rrrenai/wave/journal_images/11-8-25.png

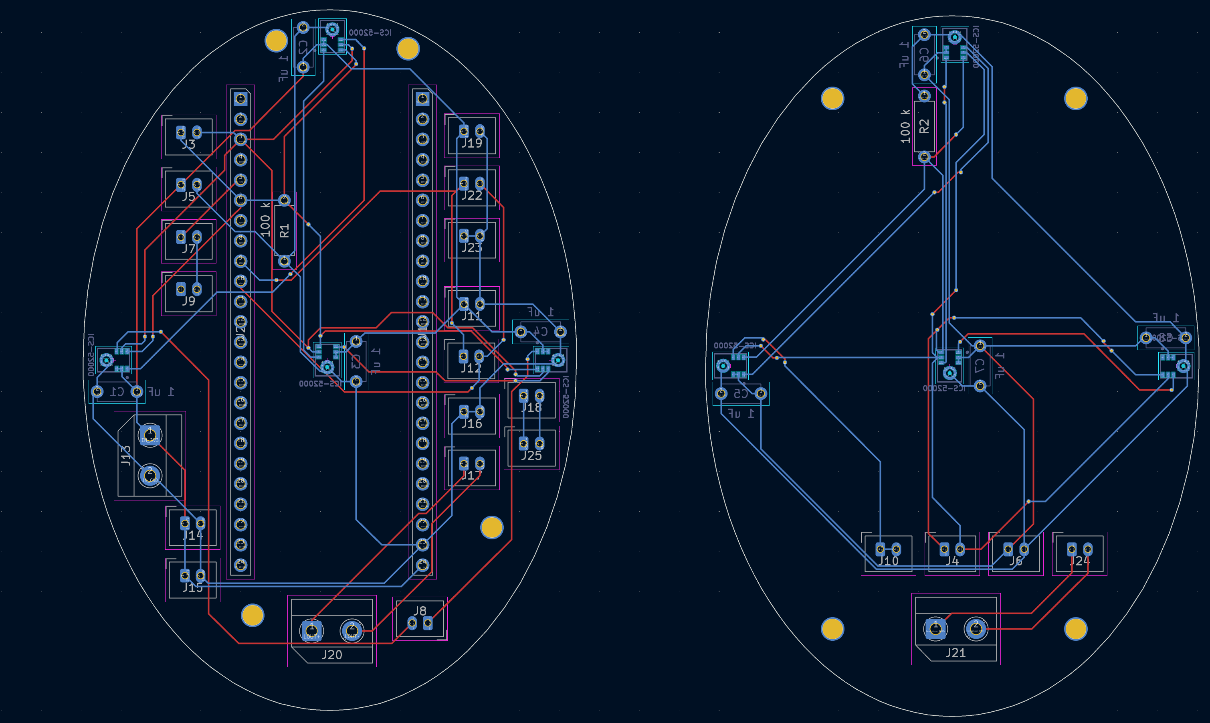
journal_images/11-8-25.png
