rrrenai/wave/journal_images/11-8-25_3d_back.png

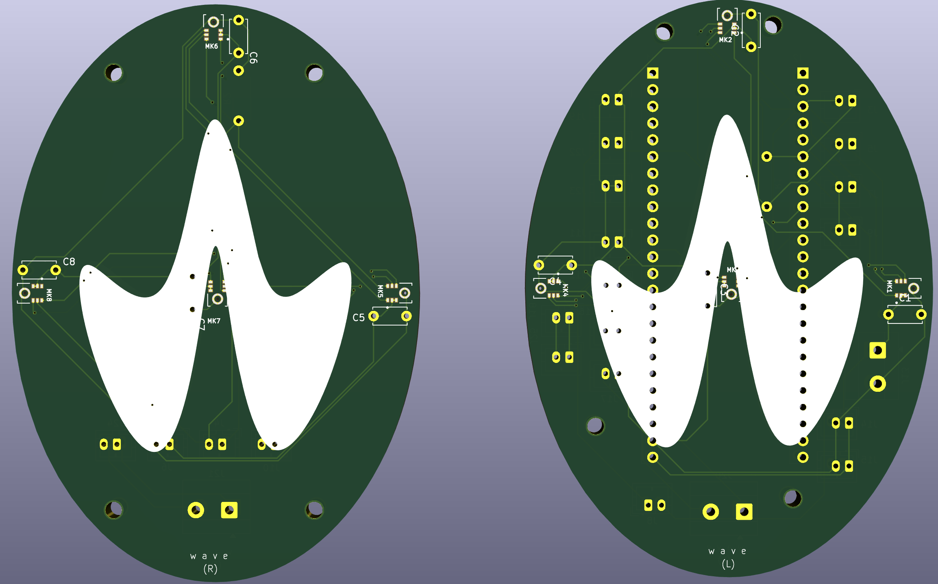
journal_images/11-8-25_3d_back.png
