rrrenai/wave/journal_images/11-20-25.png

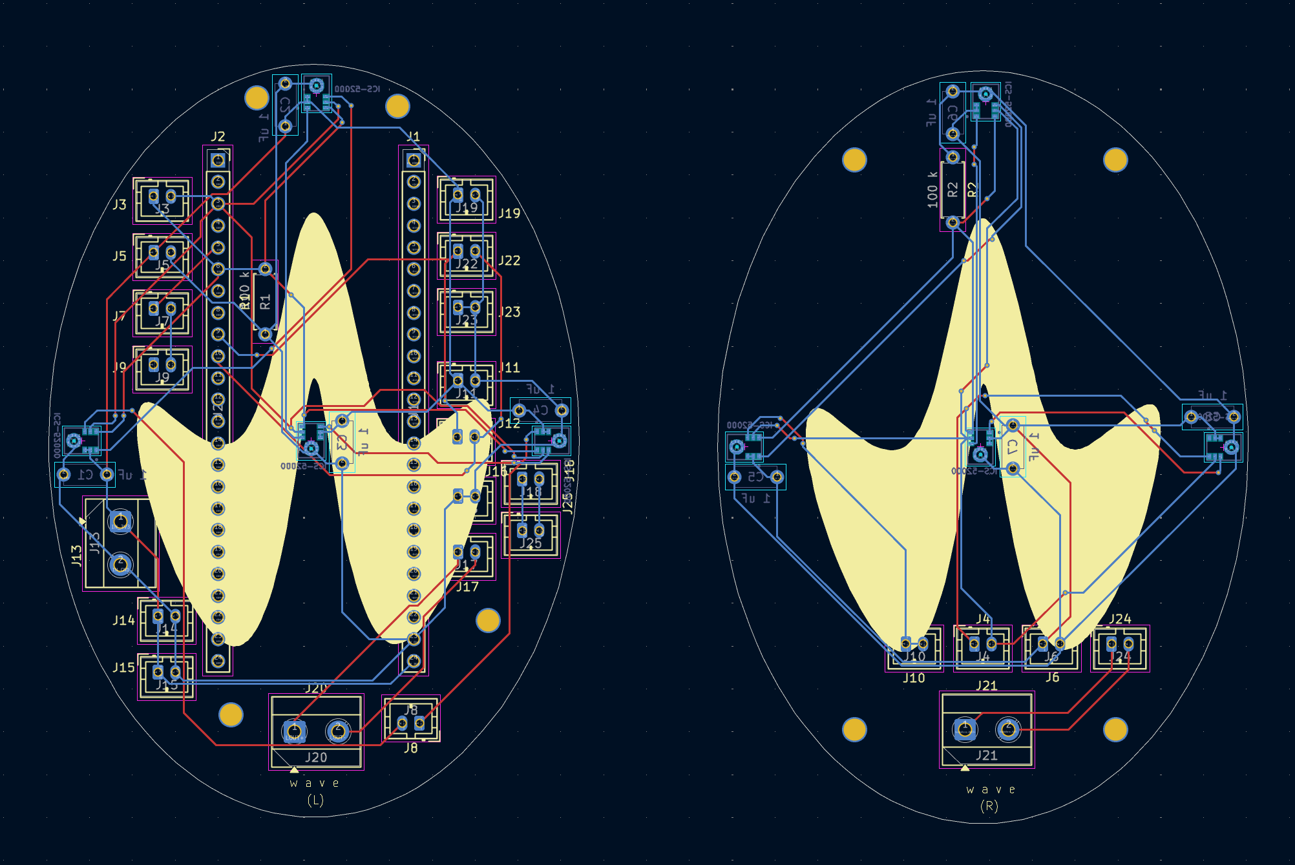
journal_images/11-20-25.png
