rrrenai/wave/journal_images/12-26-25_inner_RIGHT.png

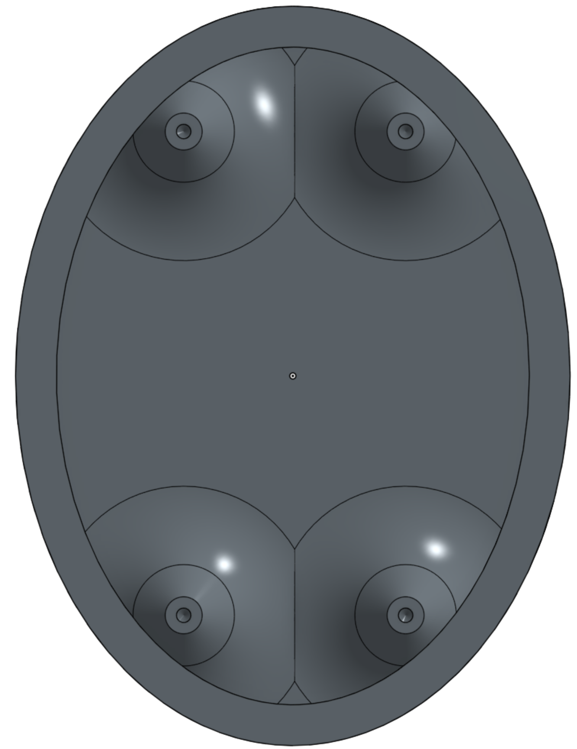
journal_images/12-26-25_inner_RIGHT.png
