rrrenai/wave/journal_images/12-26-25_SNR.png

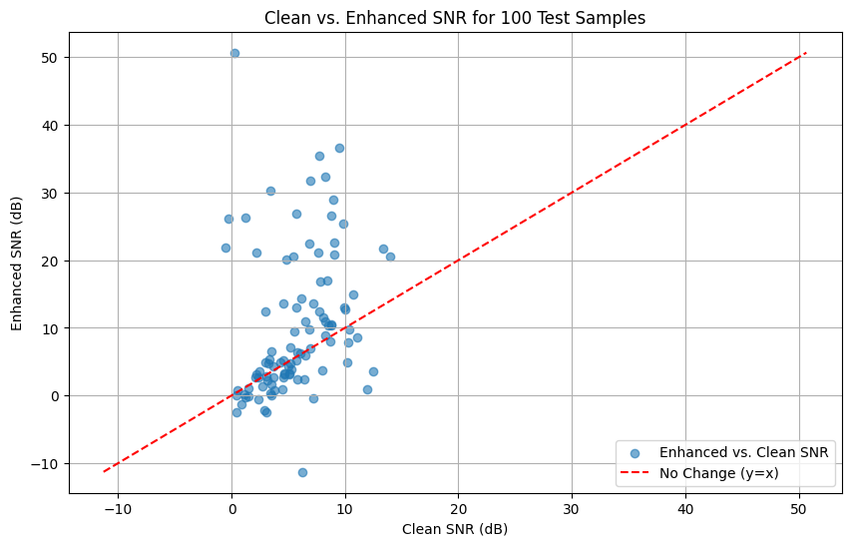
journal_images/12-26-25_SNR.png
