rrrenai/wave/journal_images/12-26-25_SNR_bar.png

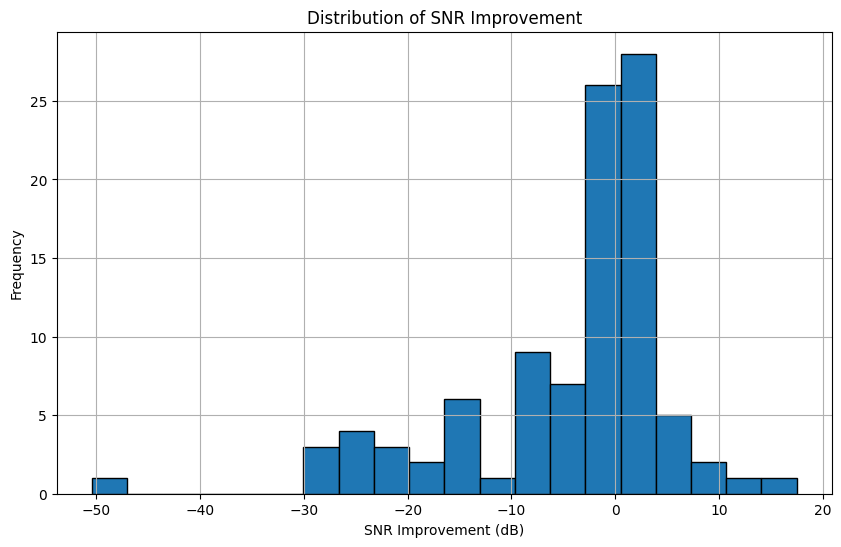
journal_images/12-26-25_SNR_bar.png
