rrrenai/wave/project_files/gowin/wave/FIFO_HS/impl/gwsynthesis/RTL_GAO/ao_0/gw_ao_init.v

parameter TRIG_LEVELS_INIT = 53'h00000000000000;
parameter MAX_DATA_DEPTH_INIT = 53'h000000000007ff;
parameter DATA_DEPTH_INIT = 53'h000000000007f3;
parameter NUM_WINDOWS_INIT = 53'h00000000000000;
parameter MATCH0_REG_M0_INIT = 53'h00000000000000;
parameter MATCH0_REG_M1_INIT = 53'h00000000000000;
parameter MATCH0_REG_M2_INIT = 53'h00000000000001;
parameter MATCH0_REG_CTRL_INIT = 53'h00000000000000;
parameter MATCH0_TRIG_CNT_INIT = 16'h0000;
parameter MATCH1_REG_M0_INIT = 16'h0000;
parameter MATCH1_REG_M1_INIT = 16'h0000;
parameter MATCH1_REG_M2_INIT = 16'h0000;
parameter MATCH1_REG_CTRL_INIT = 16'h0000;
parameter MATCH1_TRIG_CNT_INIT = 16'h0000;
parameter MATCH2_REG_M0_INIT = 16'h0000;
parameter MATCH2_REG_M1_INIT = 16'h0000;
parameter MATCH2_REG_M2_INIT = 16'h0000;
parameter MATCH2_REG_CTRL_INIT = 16'h0000;
parameter MATCH2_TRIG_CNT_INIT = 16'h0000;
parameter MATCH3_REG_M0_INIT = 16'h0000;
parameter MATCH3_REG_M1_INIT = 16'h0000;
parameter MATCH3_REG_M2_INIT = 16'h0000;
parameter MATCH3_REG_CTRL_INIT = 16'h0000;
parameter MATCH3_TRIG_CNT_INIT = 16'h0000;
parameter MATCH4_REG_M0_INIT = 16'h0000;
parameter MATCH4_REG_M1_INIT = 16'h0000;
parameter MATCH4_REG_M2_INIT = 16'h0000;
parameter MATCH4_REG_CTRL_INIT = 16'h0000;
parameter MATCH4_TRIG_CNT_INIT = 16'h0000;
parameter MATCH5_REG_M0_INIT = 16'h0000;
parameter MATCH5_REG_M1_INIT = 16'h0000;
parameter MATCH5_REG_M2_INIT = 16'h0000;
parameter MATCH5_REG_CTRL_INIT = 16'h0000;
parameter MATCH5_TRIG_CNT_INIT = 16'h0000;
parameter MATCH6_REG_M0_INIT = 16'h0000;
parameter MATCH6_REG_M1_INIT = 16'h0000;
parameter MATCH6_REG_M2_INIT = 16'h0000;
parameter MATCH6_REG_CTRL_INIT = 16'h0000;
parameter MATCH6_TRIG_CNT_INIT = 16'h0000;
parameter MATCH7_REG_M0_INIT = 16'h0000;
parameter MATCH7_REG_M1_INIT = 16'h0000;
parameter MATCH7_REG_M2_INIT = 16'h0000;
parameter MATCH7_REG_CTRL_INIT = 16'h0000;
parameter MATCH7_TRIG_CNT_INIT = 16'h0000;
parameter MATCH8_REG_M0_INIT = 16'h0000;
parameter MATCH8_REG_M1_INIT = 16'h0000;
parameter MATCH8_REG_M2_INIT = 16'h0000;
parameter MATCH8_REG_CTRL_INIT = 16'h0000;
parameter MATCH8_TRIG_CNT_INIT = 16'h0000;
parameter MATCH9_REG_M0_INIT = 16'h0000;
parameter MATCH9_REG_M1_INIT = 16'h0000;
parameter MATCH9_REG_M2_INIT = 16'h0000;
parameter MATCH9_REG_CTRL_INIT = 16'h0000;
parameter MATCH9_TRIG_CNT_INIT = 16'h0000;
parameter MATCH10_REG_M0_INIT = 16'h0000;
parameter MATCH10_REG_M1_INIT = 16'h0000;
parameter MATCH10_REG_M2_INIT = 16'h0000;
parameter MATCH10_REG_CTRL_INIT = 16'h0000;
parameter MATCH10_TRIG_CNT_INIT = 16'h0000;
parameter MATCH11_REG_M0_INIT = 16'h0000;
parameter MATCH11_REG_M1_INIT = 16'h0000;
parameter MATCH11_REG_M2_INIT = 16'h0000;
parameter MATCH11_REG_CTRL_INIT = 16'h0000;
parameter MATCH11_TRIG_CNT_INIT = 16'h0000;
parameter MATCH12_REG_M0_INIT = 16'h0000;
parameter MATCH12_REG_M1_INIT = 16'h0000;
parameter MATCH12_REG_M2_INIT = 16'h0000;
parameter MATCH12_REG_CTRL_INIT = 16'h0000;
parameter MATCH12_TRIG_CNT_INIT = 16'h0000;
parameter MATCH13_REG_M0_INIT = 16'h0000;
parameter MATCH13_REG_M1_INIT = 16'h0000;
parameter MATCH13_REG_M2_INIT = 16'h0000;
parameter MATCH13_REG_CTRL_INIT = 16'h0000;
parameter MATCH13_TRIG_CNT_INIT = 16'h0000;
parameter MATCH14_REG_M0_INIT = 16'h0000;
parameter MATCH14_REG_M1_INIT = 16'h0000;
parameter MATCH14_REG_M2_INIT = 16'h0000;
parameter MATCH14_REG_CTRL_INIT = 16'h0000;
parameter MATCH14_TRIG_CNT_INIT = 16'h0000;
parameter MATCH15_REG_M0_INIT = 16'h0000;
parameter MATCH15_REG_M1_INIT = 16'h0000;
parameter MATCH15_REG_M2_INIT = 16'h0000;
parameter MATCH15_REG_CTRL_INIT = 16'h0000;
parameter MATCH15_TRIG_CNT_INIT = 16'h0000;
